eryjus/bb-computer-v2/kicad/20-Upper-Program-Counter/program-counter-module.kicad_sch

## KiCad design kicad/20-Upper-Program-Counter/program-counter-module.kicad_sch (2022-01-30)

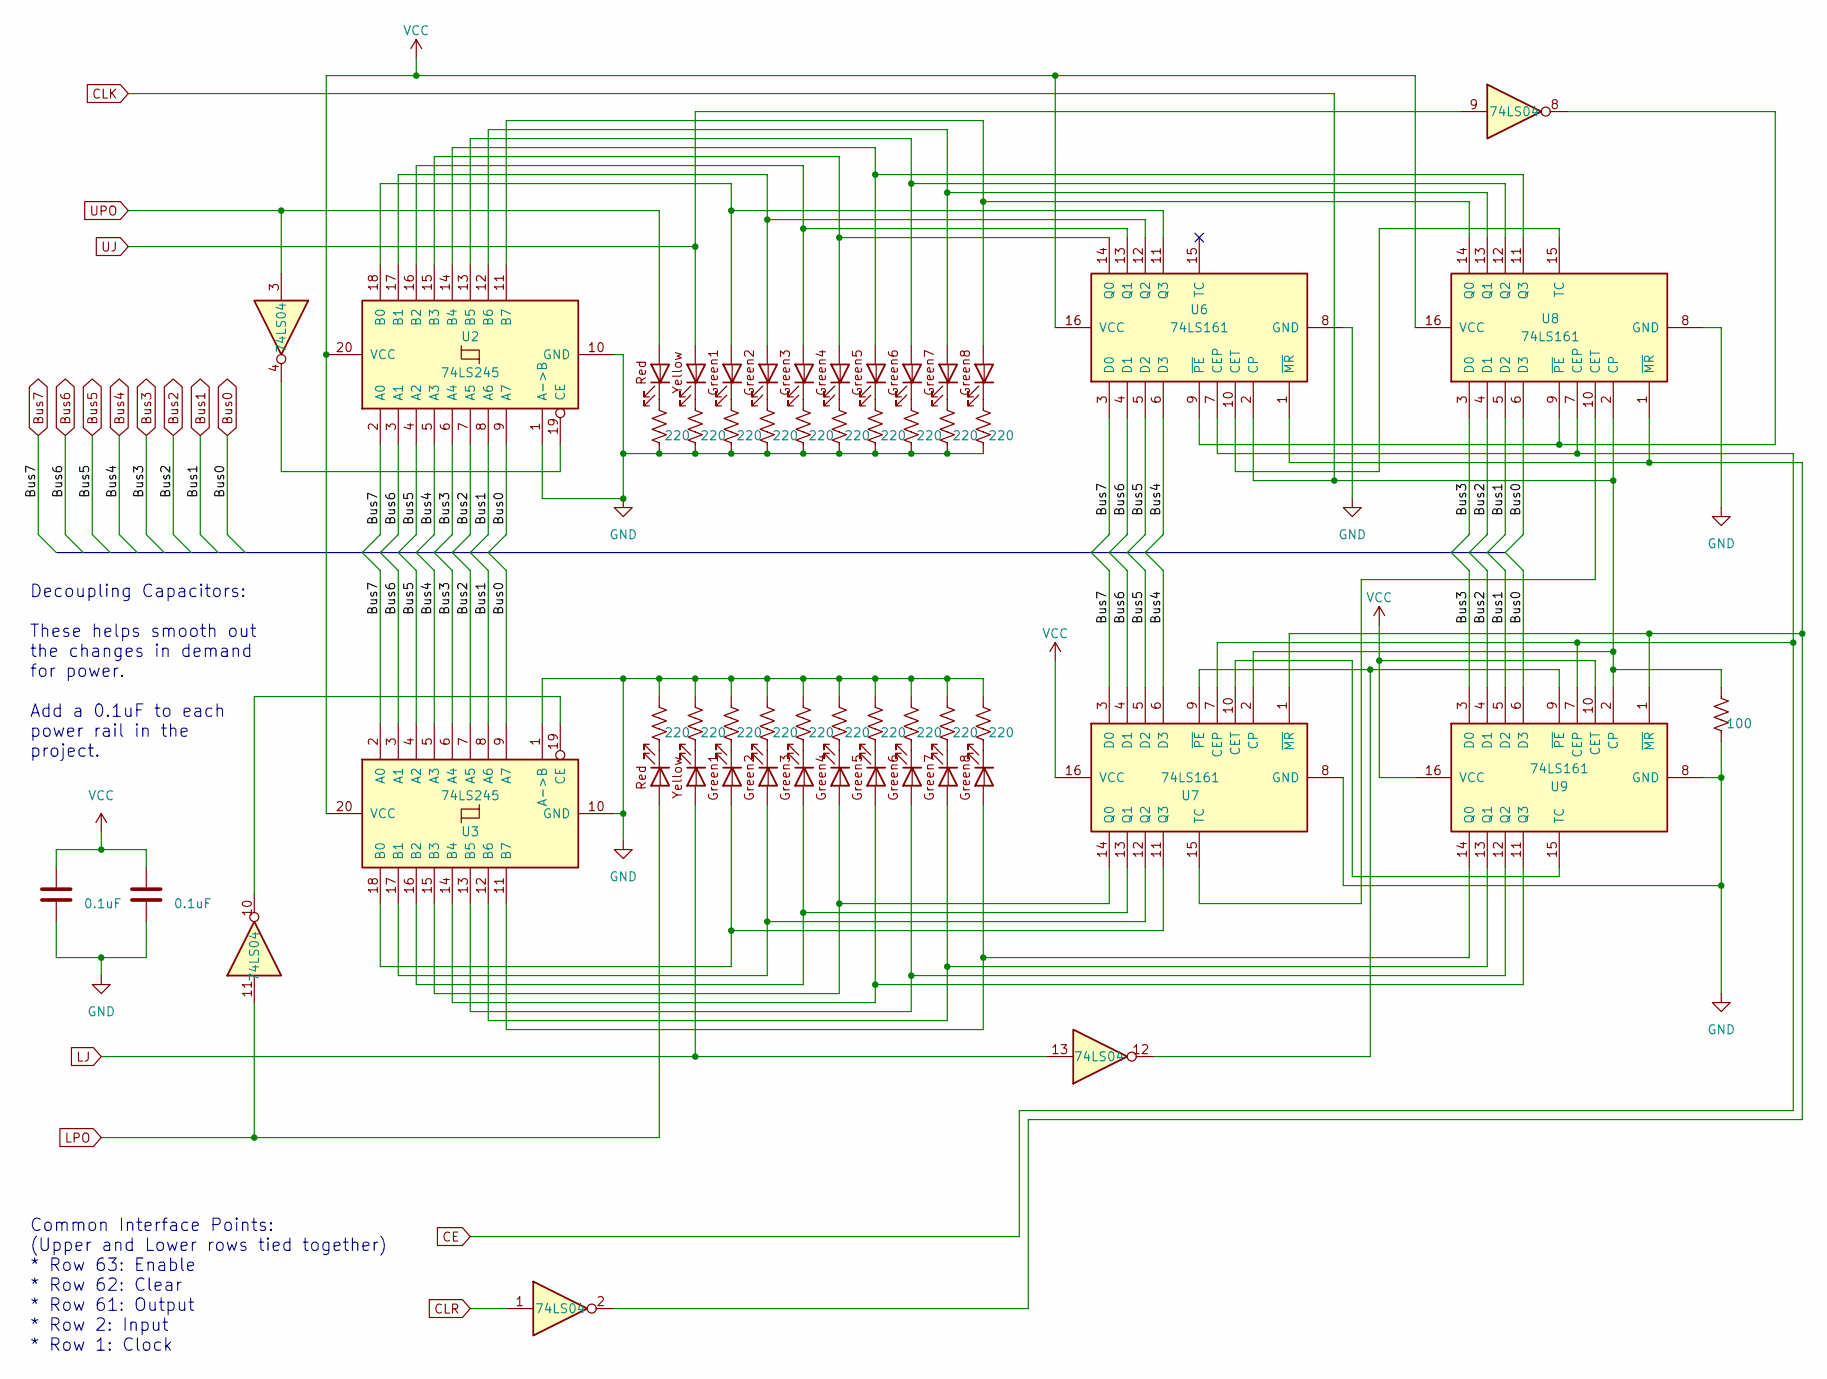
[picture p79: schematic program-counter-module.kicad_sch]

Parts:
R1, R2, R3, R4, R5, R6, R7, R8, R9, R10, R11, R12, R13, R14, R15, R16, R17, R18, R19, R20: 220
R21: 100
U1: 74LS04
U2, U3: 74LS245
U4, U5: SB1R1Y8G_LED
U6, U7, U8, U9: 74LS161

Connections:
Bus0: U2.9 (A7), U3.9 (A7), U8.6 (D3), U9.6 (D3)
Bus1: U2.8 (A6), U3.8 (A6), U8.5 (D2), U9.5 (D2)
Bus2: U2.7 (A5), U3.7 (A5), U8.4 (D1), U9.4 (D1)
Bus3: U2.6 (A4), U3.6 (A4), U8.3 (D0), U9.3 (D0)
Bus4: U2.5 (A3), U3.5 (A3), U6.6 (D3), U7.6 (D3)
Bus5: U2.4 (A2), U3.4 (A2), U6.5 (D2), U7.5 (D2)
Bus6: U2.3 (A1), U3.3 (A1), U6.4 (D1), U7.4 (D1)
Bus7: U2.2 (A0), U3.2 (A0), U6.3 (D0), U7.3 (D0)
CE: U6.7 (CEP), U7.7 (CEP), U8.7 (CEP), U9.7 (CEP)
CLK: R21.1, U6.2 (CP), U7.2 (CP), U8.2 (CP), U9.2 (CP)
GND: R1.2, R2.1, R3.2, R4.1, R5.2, R6.1, R7.2, R8.1, R9.2, R10.1, R11.2, R12.1, R13.2, R14.1, R15.2, R16.1, R17.2, R18.1, R19.2, R20.1, R21.2, U2.1 (A->B), U2.10 (GND), U3.1 (A->B), U3.10 (GND), U6.8 (GND), U7.8 (GND), U8.8 (GND), U9.8 (GND)
LJ: U1.13, U5.12
LPO: U1.11, U5.11
unnamed: R1.1, U4.1
unnamed: R2.2, U5.1
unnamed: R3.1, U4.2
unnamed: R4.2, U5.2
unnamed: R5.1, U4.3
unnamed: R6.2, U5.3
unnamed: R7.1, U4.4
unnamed: R8.2, U5.4
unnamed: R9.1, U4.5
unnamed: R10.2, U5.5
unnamed: R11.1, U4.6
unnamed: R12.2, U5.6
unnamed: R13.1, U4.7
unnamed: R14.2, U5.7
unnamed: R15.1, U4.8
unnamed: R16.2, U5.8
unnamed: R17.1, U4.9
unnamed: R18.2, U5.9
unnamed: R19.1, U4.20
unnamed: R20.2, U5.20
unnamed: U1.4, U2.19 (CE)
unnamed: U1.8, U6.9 (~PE), U8.9 (~PE)
unnamed: U1.10, U3.19 (CE)
unnamed: U1.12, U7.9 (~PE), U9.9 (~PE)
unnamed: U2.11 (B7), U4.10, U8.14 (Q0)
unnamed: U2.12 (B6), U4.19, U8.13 (Q1)
unnamed: U2.13 (B5), U4.18, U8.12 (Q2)
unnamed: U2.14 (B4), U4.17, U8.11 (Q3)
unnamed: U2.15 (B3), U4.16, U6.14 (Q0)
unnamed: U2.16 (B2), U4.15, U6.13 (Q1)
unnamed: U2.17 (B1), U4.14, U6.12 (Q2)
unnamed: U2.18 (B0), U4.13, U6.11 (Q3)
unnamed: U3.11 (B7), U5.10, U9.14 (Q0)
unnamed: U3.12 (B6), U5.19, U9.13 (Q1)
unnamed: U3.13 (B5), U5.18, U9.12 (Q2)
unnamed: U3.14 (B4), U5.17, U9.11 (Q3)
unnamed: U3.15 (B3), U5.16, U7.14 (Q0)
unnamed: U3.16 (B2), U5.15, U7.13 (Q1)
unnamed: U3.17 (B1), U5.14, U7.12 (Q2)
unnamed: U3.18 (B0), U5.13, U7.11 (Q3)
unnamed: U6.1 (~MR), U7.1 (~MR), U8.1 (~MR), U9.1 (~MR)
unnamed: U6.10 (CET), U8.15 (TC)
unnamed: U7.10 (CET), U9.15 (TC)
unnamed: U7.15 (TC), U8.10 (CET)
UJ: U1.9, U4.12
UPO: U1.3, U4.11
VCC: U2.20 (VCC), U3.20 (VCC), U6.16 (VCC), U7.16 (VCC), U8.16 (VCC), U9.10 (CET), U9.16 (VCC)

Notes on the sheet:
Common Interface Points: (Upper and Lower rows tied together) * Row 63: Enable * Row 62: Clear * Row 61: Output * Row 2: Input * Row 1: Clock
Decoupling Capacitors: These helps smooth out the changes in demand for power. Add a 0.1uF to each power rail in the project.
